BoujeeEnjinia1701/breathebox/cad/drawings/BBX-DWG-001.pdf

CONCEPT, NOT FOR FABRICATION | BreatheBox · github.com/BoujeeEnjinia1701/breathebox

FRONT VIEW
Scale 1:20; looking at the front (along +Y)

TOP VIEW
Scale 1:20; looking down (along -Z)

RIGHT VIEW
Scale 1:20; looking at the right side (along -X)

735

900 790

ISOMETRIC VIEW
Not to scale; adapter not shown; seen from the front right and above, about 30 deg elevation

KEY DIMENSIONS AND INTERFACES (MM)
Housing 510 x 560 x 250; 110 on sill, 400 into room Front view: outdoors at left; inner wall face at X = 0 Core 300 x 180 x 180, plate pitch 2.5
Insert panel 20 thick x 260 high, trims to 700 to 1000 Ports 150 x 170 at Y = +/-185
Hood mouths 130 wide, 420 clear; outer edge +/-340 Supply filter ePM1 50 % 150 x 170 x 25; exhaust G3 pad Fans 120 x 120 x 32 blowers, 24 V PWM with tach
Flow 30 to 70 m3/h per stream, 50 nominal, 32 night mode
Core frames, dividers and fan bulkhead seal the four air paths Tray drain at floor level, 12 x 8 tube through panel
Rails, struts and padded foot prop on the wall; foot 400 above floor Sash jammer (item 14) above the raised sash; not shown
Mass about 11.8 kg installed; build plan BBX-BLD-001 PRELIMINARY, NOT FOR FABRICATION
REV | DESCRIPTION | DATE | BY
P1 | Preliminary GA for TRL 3 (BBX-CAL-001) | 2026-09-25 | AC
P2 | Night mode note (BBX-DDR-002) | 2026-09-25 | AC
P3 | Constructable design (BBX-DDR-003) | 2026-09-30 | AC
P4 | Wall foot at 400; sash jammer (BBX-DEC-001) | 2026-10-02 | AC
BREATHEBOX | github.com/BoujeeEnjinia1701/breathebox

## General arrangement, window HRV

DRAWING NO.
BBX-DWG-001

REV
P4

SHEET
1 of 1

SIZE

## ANSI B

SCALE
1:20

UNITS
mm
PROJECTION | DATE
2026-10-02

DRAWN
Amish Chadha

MATERIAL / NOTES
Housing 6 mm PVC foam board, battens, foam lining; panel PVC/XPS; hoods PVC; bracket Al. See bom/bom.csv
Licensed CERN-OHL-S-2.0 · Design Molecule Lab · designmolecule.com | Generated from cad/src; do not edit by hand
