BoujeeEnjinia1701/breathebox/cad/drawings/BBX-DWG-111.pdf

BUILD PLAN SKETCH, PLAN NOT YET BUILT BreatheBox · github.com/BoujeeEnjinia1701/breathebox

FRONT VIEW
Scale 1:5; looking at the front (along +Y)

TOP VIEW
Scale 1:5; looking down (along -Z)

RIGHT VIEW
Scale 1:5; looking at the right side (along -X)

390

50 44

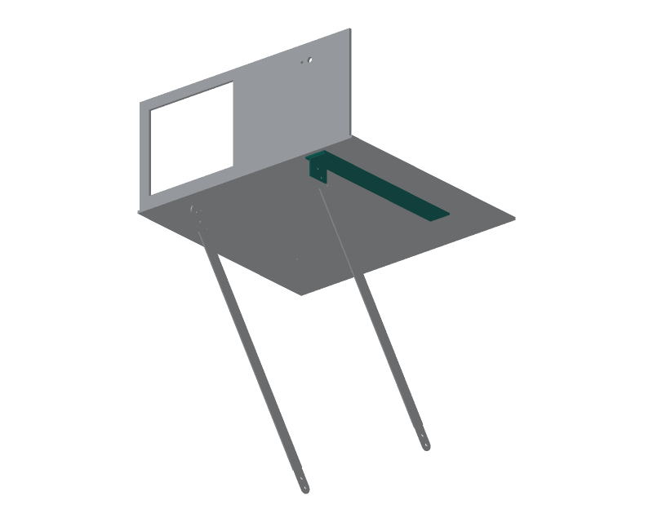
[picture p7: figure]

WHERE IT GOES
This part in colour, its neighbours in grey

HOW TO MAKE IT AND HOW IT FITS
Rail: 50 x 4 aluminium flat bar, 390 long. Round the corners.
Two 5.5 holes for the housing bolts, 30 and 330 from the wall end, 25 in from the rail's inner edge.
Two 5.5 holes countersunk from the top for the cleat, 348 and 378 from the wall end, 31 in from the inner edge.
Cleat: 40 x 40 x 3 angle, 50 long. Flat leg under the rail, 338 to 388 from the wall end, holes matching the rail. Upright leg on the rail's inner side: two 6.6 holes, 27 and 15.5 from the cleat's wall-side end, 16 and 32.4 down from the rail's underside. Drill the strut holes with the strut clamped in place (sketch 112). Fit: the rail bolts under the housing base with two M5 bolts, nuts inside under the floor lining; its wall end is flush with the housing's line on the wall face.
REV | DESCRIPTION | DATE | BY
P1 | Making sketch for the prototype build plan | 2026-09-30 | AC
P2 | Wall foot at 400 mm, longer struts (BBX-DEC-001) | 2026-10-02 | AC
BREATHEBOX | github.com/BoujeeEnjinia1701/breathebox

## BreatheBox bracket rail with its top cleat (make 2): making sketch

DRAWING NO.
BBX-DWG-111

REV
P2

SHEET
1 of 1

SIZE

## ANSI B

SCALE
1:5

UNITS
mm
PROJECTION | DATE
2026-10-02

DRAWN
Amish Chadha

MATERIAL / NOTES
Aluminium flat bar 50 x 4; equal angle 40 x 40 x 3
Licensed CERN-OHL-S-2.0 · Design Molecule Lab · designmolecule.com | Generated from cad/src; do not edit by hand
