BoujeeEnjinia1701/breathebox/cad/drawings/BBX-DWG-112.pdf

BUILD PLAN SKETCH, PLAN NOT YET BUILT BreatheBox · github.com/BoujeeEnjinia1701/breathebox

FRONT VIEW
Scale 1:5; looking at the front (along +Y)

TOP VIEW
Scale 1:5; looking down (along -Z)

RIGHT VIEW
Scale 1:5; looking at the right side (along -X)

621

26 20

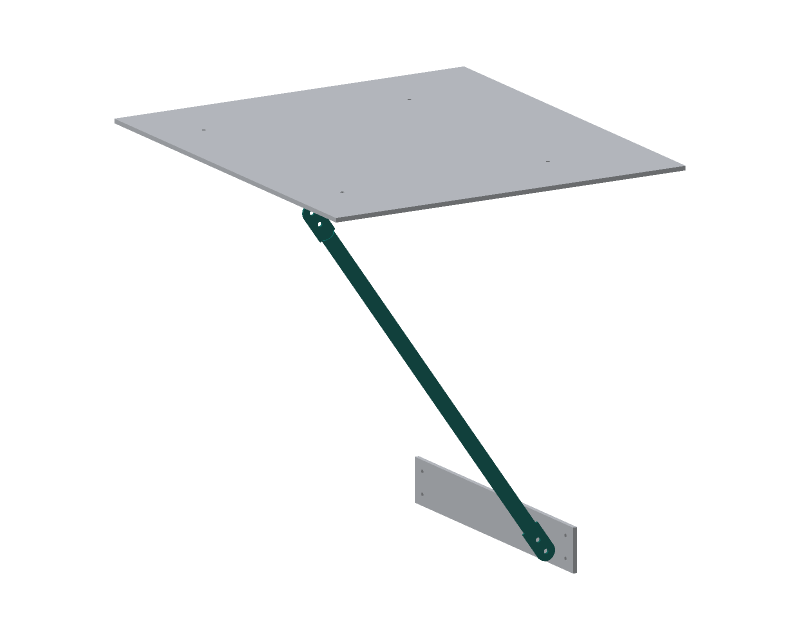
[picture p8: figure]

WHERE IT GOES
This part in colour, its neighbours in grey

HOW TO MAKE IT AND HOW IT FITS
Tube 20 x 1.5, cut 621 long.
Flatten 40 of each end in a vice between two flat bars, both flats in the same plane; anneal with a gas torch first if it cracks.
Trim each flat to 26 wide and round its end to a 13 radius about the end hole.
End holes 6.6, 595.3 apart; a second 6.6 hole 20 in
from each end hole, on the centre line. Two holes at each end make the joints rigid, so the bracket cannot fold.
The strut rises at 55 degrees from the wall foot to the rail. Drill the second pair with the strut clamped to both cleats, so all four holes line up.
Fit: M6 bolts, heads on the strut side, nyloc nuts on the cleats. Check: end holes within 0.5 of the length; flats not twisted.
REV | DESCRIPTION | DATE | BY
P1 | Making sketch for the prototype build plan | 2026-09-30 | AC
P2 | Wall foot at 400 mm, longer struts (BBX-DEC-001) | 2026-10-02 | AC
BREATHEBOX | github.com/BoujeeEnjinia1701/breathebox

## BreatheBox strut (make 2): making sketch

DRAWING NO.
BBX-DWG-112

REV
P2

SHEET
1 of 1

SIZE

## ANSI B

SCALE
1:5

UNITS
mm
PROJECTION | DATE
2026-10-02

DRAWN
Amish Chadha

MATERIAL / NOTES
Aluminium round tube 20 x 1.5 mm, 6063 class
Licensed CERN-OHL-S-2.0 · Design Molecule Lab · designmolecule.com | Generated from cad/src; do not edit by hand
