BoujeeEnjinia1701/breathebox/cad/drawings/BBX-DWG-113.pdf

BUILD PLAN SKETCH, PLAN NOT YET BUILT BreatheBox · github.com/BoujeeEnjinia1701/breathebox

FRONT VIEW
Scale 1:5; looking at the front (along +Y)

TOP VIEW
Scale 1:5; looking down (along -Z)

RIGHT VIEW
Scale 1:5; looking at the right side (along -X)

400

48 60

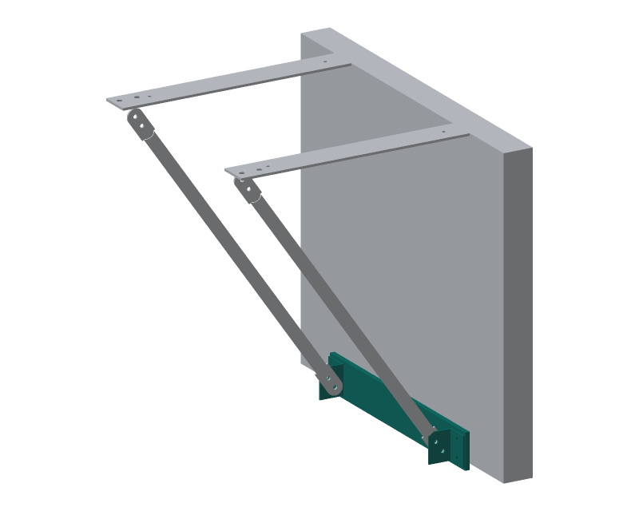
[picture p9: figure]

WHERE IT GOES
This part in colour, its neighbours in grey

HOW TO MAKE IT AND HOW IT FITS
Bar: 60 x 6 aluminium flat bar, 400 long. Four 5.5 holes, 181 each side of centre, 15 above and below its centre line, countersunk from the wall side so the screw heads sit flush.
Pad: 2 mm rubber sheet 400 x 60, glued to the wall side, with relief holes over the screw heads.
Cleats: 40 x 40 x 3 angle, 50 long. One leg on the bar's room face, holes matching the bar; the other leg points into the room, on the inner side, with two 6.6 holes 16 and 27.5 out from the bar face, 17 and 33.4 up from the cleat's lower end.
Fit: the foot's centre line is 400 above the floor; the pad presses on the wall; nothing is fixed to the wall.
Check: the pad lies flat on the wall over its whole length.
REV | DESCRIPTION | DATE | BY
P1 | Making sketch for the prototype build plan | 2026-09-30 | AC
P2 | Wall foot at 400 mm, longer struts (BBX-DEC-001) | 2026-10-02 | AC
BREATHEBOX | github.com/BoujeeEnjinia1701/breathebox

## BreatheBox wall foot with pad and foot cleats: making sketch

DRAWING NO.
BBX-DWG-113

REV
P2

SHEET
1 of 1

SIZE

## ANSI B

SCALE
1:5

UNITS
mm
PROJECTION | DATE
2026-10-02

DRAWN
Amish Chadha

MATERIAL / NOTES
Aluminium flat bar 60 x 6; angle 40 x 40 x 3; rubber 2 mm
Licensed CERN-OHL-S-2.0 · Design Molecule Lab · designmolecule.com | Generated from cad/src; do not edit by hand
