BoujeeEnjinia1701/breathebox/cad/drawings/BBX-DWG-101.pdf

BUILD PLAN SKETCH, PLAN NOT YET BUILT BreatheBox · github.com/BoujeeEnjinia1701/breathebox

FRONT VIEW
Scale 1:10; looking at the front (along +Y)

TOP VIEW
Scale 1:10; looking down (along -Z)

RIGHT VIEW
Scale 1:10; looking at the right side (along -X)

510

560 244

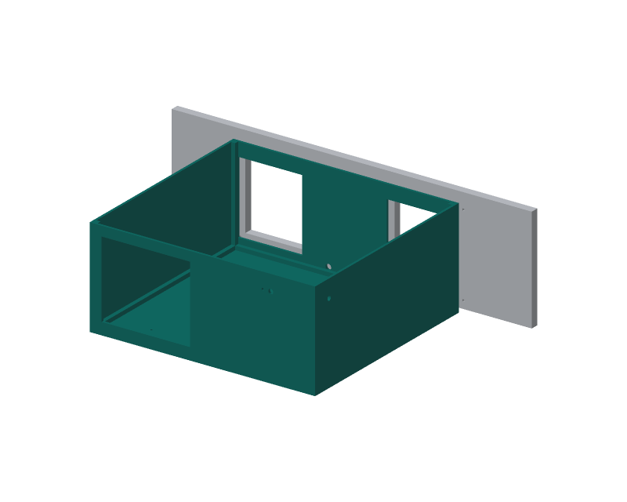
[picture p51: figure]

WHERE IT GOES
This part in colour, its neighbours in grey

HOW TO MAKE IT AND HOW IT FITS
Cut from 6 mm PVC foam board: base 510 x 560; two sides 510 x 238; two ends 548 x 238. Ends fit between the sides; all stand on the base. Outdoor end: two 160 x 180 openings centred 185 left and right, from 24 to 204 up from its bottom edge; a 14 hole 40 left, 16 up. Room end: a 220 x 190 opening from 30 to 250 left, 24 to 214 up; holes 6 and 12 at 150 and 170 right, 199 up (light and button).
Right side: a 12 hole 50 from the room end, 194 up (power gland). Base: four 5.5 holes, 140 and 440 from the outdoor edge, 175 each side. Battens 10 x 10: four uprights 238; two 478 under the sides; two 528 under the ends. Glue every joint with PVC cement and screw each board into the batten behind it, 3.5 x 16 screws at 80 centres.
Check: square within 1 mm on the diagonals; openings line up with the collar and grille positions on the other sketches.
REV | DESCRIPTION | DATE | BY
P1 | Making sketch for the prototype build plan | 2026-09-30 | AC
BREATHEBOX | github.com/BoujeeEnjinia1701/breathebox

## BreatheBox housing boards and battens: making sketch

DRAWING NO.
BBX-DWG-101

REV
P1

SHEET
1 of 1

SIZE

## ANSI B

SCALE
1:10

UNITS
mm
PROJECTION | DATE
2026-09-30

DRAWN
Amish Chadha

MATERIAL / NOTES
6 mm PVC foam board; 10 x 10 mm PVC or pine strip
Licensed CERN-OHL-S-2.0 · Design Molecule Lab · designmolecule.com | Generated from cad/src; do not edit by hand
