BoujeeEnjinia1701/breathebox/cad/drawings/BBX-DWG-102.pdf

BUILD PLAN SKETCH, PLAN NOT YET BUILT BreatheBox · github.com/BoujeeEnjinia1701/breathebox

FRONT VIEW
Scale 1:5; looking at the front (along +Y)

TOP VIEW
Scale 1:5; looking down (along -Z)

RIGHT VIEW
Scale 1:5; looking at the right side (along -X)

510

580 46

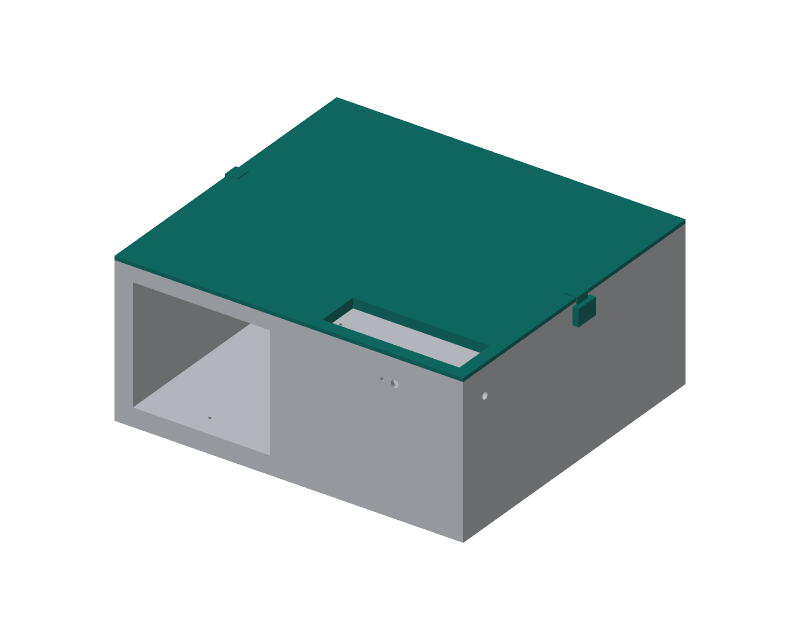
[picture p52: figure]

WHERE IT GOES
This part in colour, its neighbours in grey

HOW TO MAKE IT AND HOW IT FITS
Board 510 x 560 x 6 mm. Opening 70 x 220 for the supply grille,
420 to 490 from the outdoor edge, 40 to 260 right of centre.
Lining plug: 10 mm foam, 476 x 526, glued centred under the board so it drops inside the wall lining with 1 mm all round; cut the same
70 x 220 opening through it.
Foam blocks glued under the plug (they hold the core and filters): core hold-down 306 long x 168 wide x 24 deep, over the core; supply filter block 34 x 138 x 28 at the outdoor end, right; exhaust filter block 21 x 200 x 18 at the room end, left.
Latch keepers: one each side, 118 to 142 from the outdoor edge. Check: the lid drops on with the plug inside the walls and the latches pull it down evenly onto the gasket tape.
REV | DESCRIPTION | DATE | BY
P1 | Making sketch for the prototype build plan | 2026-09-30 | AC
BREATHEBOX | github.com/BoujeeEnjinia1701/breathebox

## BreatheBox lid: making sketch

DRAWING NO.
BBX-DWG-102

REV
P1

SHEET
1 of 1

SIZE

## ANSI B

SCALE
1:5

UNITS
mm
PROJECTION | DATE
2026-09-30

DRAWN
Amish Chadha

MATERIAL / NOTES
6 mm PVC foam board; 10 mm closed-cell foam
Licensed CERN-OHL-S-2.0 · Design Molecule Lab · designmolecule.com | Generated from cad/src; do not edit by hand
