BoujeeEnjinia1701/breathebox/cad/drawings/BBX-DWG-103.pdf

BUILD PLAN SKETCH, PLAN NOT YET BUILT BreatheBox · github.com/BoujeeEnjinia1701/breathebox

FRONT VIEW
Scale 1:5; looking at the front (along +Y)

TOP VIEW
Scale 1:5; looking down (along -Z)

RIGHT VIEW
Scale 1:5; looking at the right side (along -X)

528

3 218

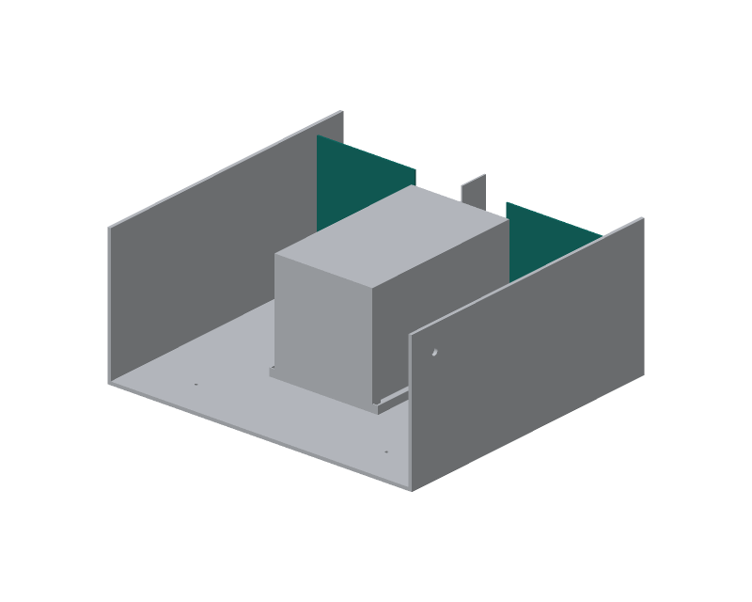
[picture p53: figure]

WHERE IT GOES
This part in colour, its neighbours in grey

HOW TO MAKE IT AND HOW IT FITS
Make two from 3 mm PVC foam board, each 528 wide x 218 tall. Cut a U 168 wide, centred, from 20 up off the bottom edge to the top. The core's 180 wide end then overlaps the U by 6 each side and 6
at the bottom; stick 3 mm foam gasket tape round the U on the
core side.
Outdoor frame only: a 13 hole 40 left of centre (as seen from the room; drawn here as seen from outdoors), 6 up, for the drain tube.
Fit: stands on the floor lining, glued to the side lining with
contact adhesive, 300 apart (inside faces) so the core fits
between them; the lid's foam block closes the U above the core. Check: the core drops between the frames without force and both ends bear on the gasket all round the U.
REV | DESCRIPTION | DATE | BY
P1 | Making sketch for the prototype build plan | 2026-09-30 | AC
BREATHEBOX | github.com/BoujeeEnjinia1701/breathebox

## BreatheBox core frame (make 2): making sketch

DRAWING NO.
BBX-DWG-103

REV
P1

SHEET
1 of 1

SIZE

## ANSI B

SCALE
1:5

UNITS
mm
PROJECTION | DATE
2026-09-30

DRAWN
Amish Chadha

MATERIAL / NOTES
3 mm PVC foam board
Licensed CERN-OHL-S-2.0 · Design Molecule Lab · designmolecule.com | Generated from cad/src; do not edit by hand
