BoujeeEnjinia1701/breathebox/cad/drawings/BBX-DWG-104.pdf

BUILD PLAN SKETCH, PLAN NOT YET BUILT BreatheBox · github.com/BoujeeEnjinia1701/breathebox

FRONT VIEW
Scale 1:2; looking at the front (along +Y)

TOP VIEW
Scale 1:2; looking down (along -Z)

RIGHT VIEW
Scale 1:2; looking at the right side (along -X)

236

3 218

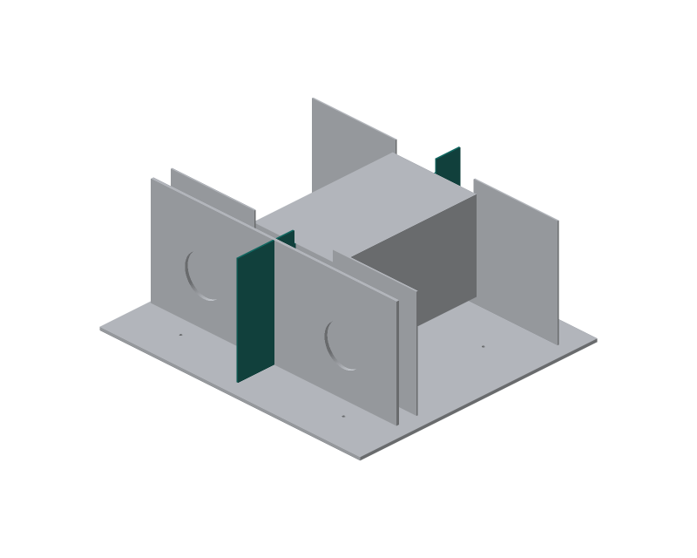
[picture p54: figure]

WHERE IT GOES
This part in colour, its neighbours in grey

HOW TO MAKE IT AND HOW IT FITS
Three pieces of 3 mm PVC foam board, all 218 tall, on the centre line. Outdoor-end divider: 51 long, plus a tongue 3 long x 174 tall,
20 up from the bottom, that reaches through the frame's U to the core face (drawn left).
Core-side divider: 37 long plus the same tongue (drawn middle). Room-side divider: 78 long, plain (drawn right).
Fit: each stands on the floor lining, glued to the frame, bulkhead or end lining it meets; the tongue's end just touches the core. The dividers split each end of the box into supply (right) and exhaust (left), so the two air streams never meet.
Check: no daylight past any divider edge with the core in.
REV | DESCRIPTION | DATE | BY
P1 | Making sketch for the prototype build plan | 2026-09-30 | AC
BREATHEBOX | github.com/BoujeeEnjinia1701/breathebox

## BreatheBox dividers (3): making sketch

DRAWING NO.
BBX-DWG-104

REV
P1

SHEET
1 of 1

SIZE

## ANSI B

SCALE
1:2

UNITS
mm
PROJECTION | DATE
2026-09-30

DRAWN
Amish Chadha

MATERIAL / NOTES
3 mm PVC foam board
Licensed CERN-OHL-S-2.0 · Design Molecule Lab · designmolecule.com | Generated from cad/src; do not edit by hand
