BoujeeEnjinia1701/breathebox/cad/drawings/BBX-DWG-105.pdf

BUILD PLAN SKETCH, PLAN NOT YET BUILT BreatheBox · github.com/BoujeeEnjinia1701/breathebox

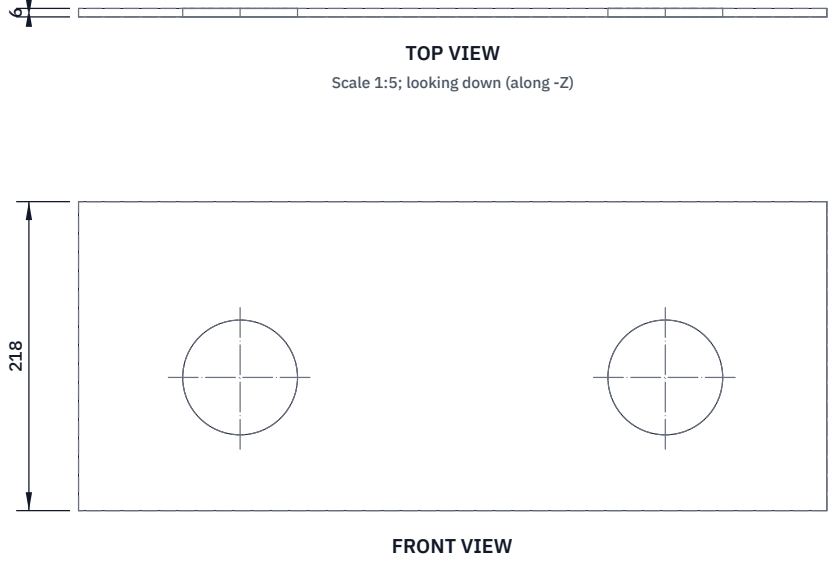
[picture p55: figure]
FRONT VIEW; TOP VIEW; Scale 1:5; looking down (along -Z)

Scale 1:5; looking at the front (along +Y)

RIGHT VIEW
Scale 1:5; looking at the right side (along -X)

528

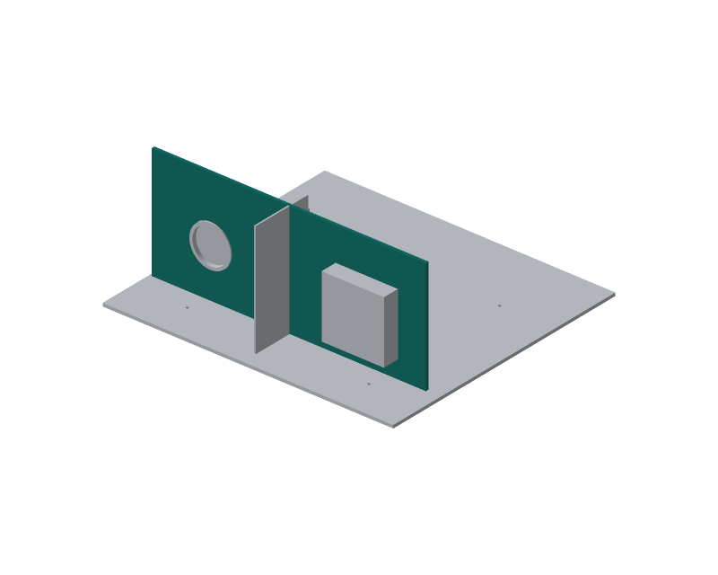
[picture p56: figure]

WHERE IT GOES
This part in colour, its neighbours in grey

HOW TO MAKE IT AND HOW IT FITS
6 mm PVC foam board, 528 wide x 218 tall.
Two 81 holes for the fan inlets, centred 150 left and 150 right of centre, 94 up from the bottom edge.
Mark each fan's four mounting holes through the fan itself; drill 5 and fit rubber grommets so the fans do not drum on the board. Fit: stands on the floor lining, its room-side face 94 from the outside of the room end (78 from the end lining), glued to the side linings. Drawn as seen from outdoors.
The supply fan (right) goes on the room side, its inlet through the hole; the exhaust fan (left) goes on the core side, its inlet through the hole facing the room. M4 nylon screws.
Check: each fan ring sits in its hole with about 0.5 mm all round.
REV | DESCRIPTION | DATE | BY
P1 | Making sketch for the prototype build plan | 2026-09-30 | AC
BREATHEBOX | github.com/BoujeeEnjinia1701/breathebox

## BreatheBox fan bulkhead: making sketch

DRAWING NO.
BBX-DWG-105

REV
P1

SHEET
1 of 1

SIZE

## ANSI B

SCALE
1:5

UNITS
mm
PROJECTION | DATE
2026-09-30

DRAWN
Amish Chadha

MATERIAL / NOTES
6 mm PVC foam board
Licensed CERN-OHL-S-2.0 · Design Molecule Lab · designmolecule.com | Generated from cad/src; do not edit by hand
