BoujeeEnjinia1701/breathebox/cad/drawings/BBX-DWG-106.pdf

BUILD PLAN SKETCH, PLAN NOT YET BUILT BreatheBox · github.com/BoujeeEnjinia1701/breathebox

FRONT VIEW
Scale 1:2; looking at the front (along +Y)

TOP VIEW
Scale 1:2; looking down (along -Z)

RIGHT VIEW
Scale 1:2; looking at the right side (along -X)

164

35 218

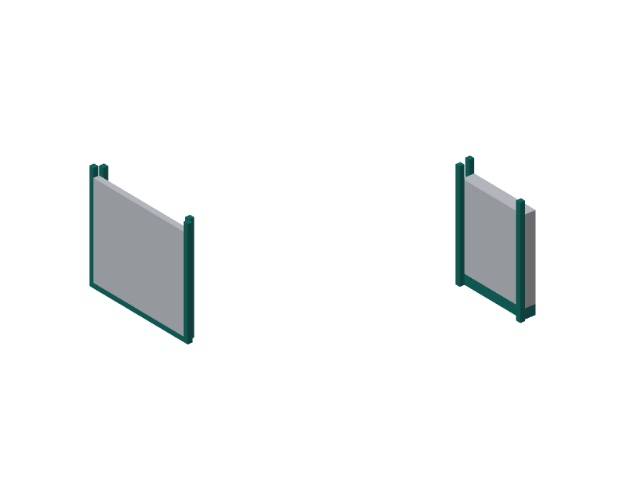
[picture p57: figure]

WHERE IT GOES
This part in colour, its neighbours in grey

HOW TO MAKE IT AND HOW IT FITS
All 10 x 10 strip, glued to the lining with contact adhesive.
Supply seat (outdoor end, right; drawn here): a side strip 218 long against the end lining beside the filter's left edge; two lip
strips 218 long 25 out from the end lining, lapping 6 over each filter edge; a bottom stop 150 x 25 x 20 under the filter.
Exhaust seat (room end, left): side strips 218 long each side of the pad against the room end lining; lip strips 12 out from it, lapping 10 over each pad edge; a bottom stop 220 x 12 x 10. The air pushes each filter onto its lips; the lid's foam blocks press on the top edges, so no air goes round a filter.
Check: each filter slides down into its seat by hand and sits square on its lips and stop.
REV | DESCRIPTION | DATE | BY
P1 | Making sketch for the prototype build plan | 2026-09-30 | AC
BREATHEBOX | github.com/BoujeeEnjinia1701/breathebox

## BreatheBox filter seat strips and stops: making sketch

DRAWING NO.
BBX-DWG-106

REV
P1

SHEET
1 of 1

SIZE

## ANSI B

SCALE
1:2

UNITS
mm
PROJECTION | DATE
2026-09-30

DRAWN
Amish Chadha

MATERIAL / NOTES
10 x 10 mm PVC or pine strip
Licensed CERN-OHL-S-2.0 · Design Molecule Lab · designmolecule.com | Generated from cad/src; do not edit by hand
