BoujeeEnjinia1701/breathebox/cad/drawings/BBX-DWG-107.pdf

BUILD PLAN SKETCH, PLAN NOT YET BUILT BreatheBox · github.com/BoujeeEnjinia1701/breathebox

FRONT VIEW
Scale 1:5; looking at the front (along +Y)

TOP VIEW
Scale 1:5; looking down (along -Z)

RIGHT VIEW
Scale 1:5; looking at the right side (along -X)

300

200 14

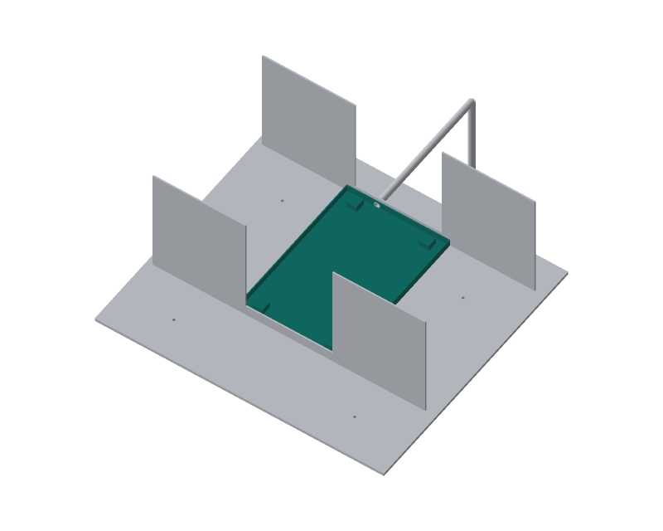
[picture p58: figure]

WHERE IT GOES
This part in colour, its neighbours in grey

HOW TO MAKE IT AND HOW IT FITS
2 mm PETG sheet. Blank 328 x 228; fold up 14 mm on all four sides (heat gun and a wooden former), so the tray is 300 x 200 x 14. Seal each corner inside with a fillet of clear silicone.
Drain hole 12 in the outdoor end wall, 40 left of centre, its
centre 6 up from the underside so the bore is flush with the floor. Four pads 20 x 20 x 12 cut from PETG offcuts stacked and glued, at the four corners, 10 in from each end and 60 out from the centre line; the core sits on them, so water runs freely underneath.
Fit: sits on the floor lining between the core frames.
Check: fill with 100 ml of water with the drain tube fitted; it all runs out with the box level, and no corner weeps.
REV | DESCRIPTION | DATE | BY
P1 | Making sketch for the prototype build plan | 2026-09-30 | AC
BREATHEBOX | github.com/BoujeeEnjinia1701/breathebox

## BreatheBox condensate tray: making sketch

DRAWING NO.
BBX-DWG-107

REV
P1

SHEET
1 of 1

SIZE

## ANSI B

SCALE
1:5

UNITS
mm
PROJECTION | DATE
2026-09-30

DRAWN
Amish Chadha

MATERIAL / NOTES
PETG sheet 2 mm
Licensed CERN-OHL-S-2.0 · Design Molecule Lab · designmolecule.com | Generated from cad/src; do not edit by hand
