BoujeeEnjinia1701/breathebox/cad/drawings/BBX-DWG-108.pdf

BUILD PLAN SKETCH, PLAN NOT YET BUILT BreatheBox · github.com/BoujeeEnjinia1701/breathebox

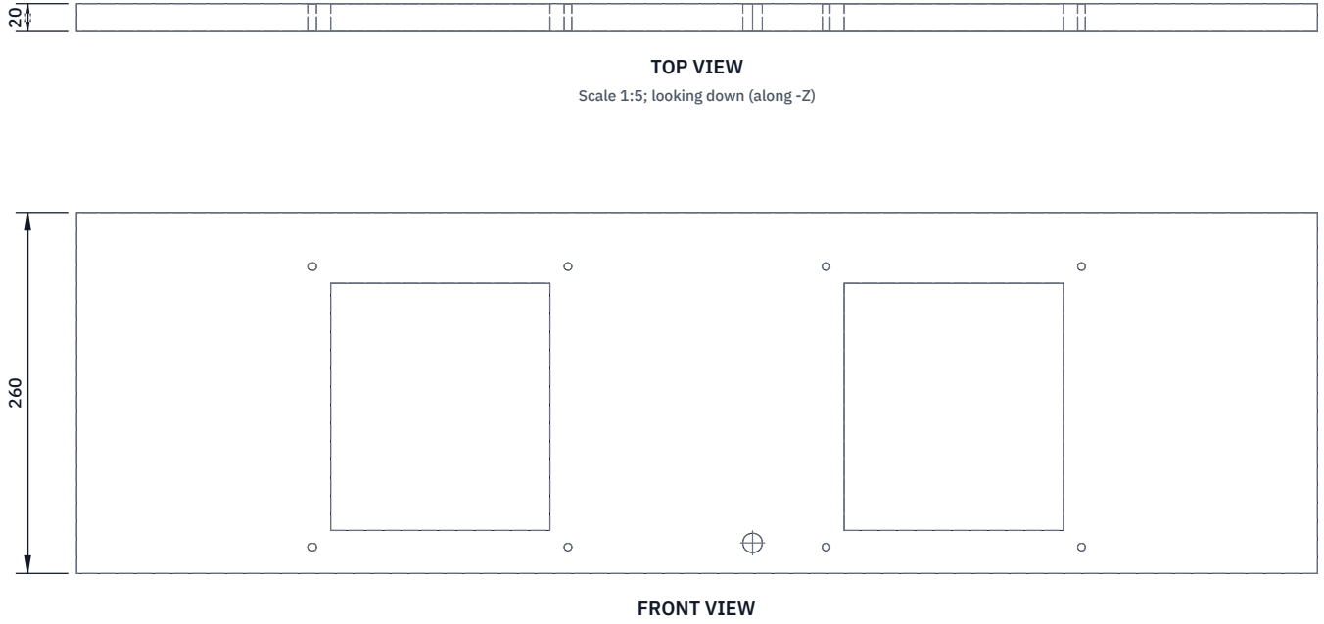
[picture p59: figure]
FRONT VIEW; TOP VIEW; Scale 1:5; looking down (along -Z)

Scale 1:5; looking at the front (along +Y)

RIGHT VIEW
Scale 1:5; looking at the right side (along -X)

894

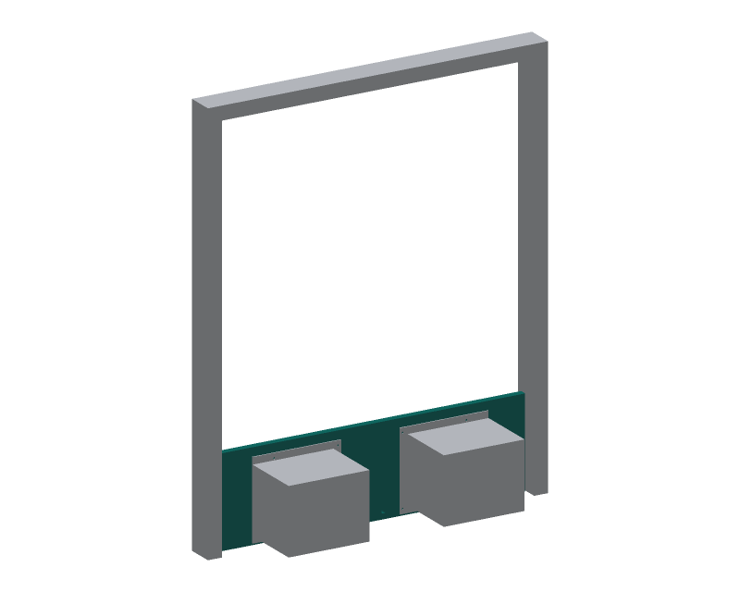
[picture p60: figure]

WHERE IT GOES
This part in colour, its neighbours in grey

HOW TO MAKE IT AND HOW IT FITS
20 mm panel, 260 tall, cut to the window's clear width less 6 (894 for a 900 window), so the EPDM seals take up 3 each end. Two 158 x 178 cut-outs centred 185 left and right of centre, from 31 to 209 up from the bottom edge.
Drain hole 14, 40 left of centre as seen from the room, 22 up (drawn as seen from outdoors, so it appears right of centre).
Bolt holes 5.5: at 93 and 277 out from centre on each side, 19 and 221 up (eight in all). Drill them through the collar flange
clamped in place, so they match.
Seal the cut edges of the XPS core with aluminium tape.
Fit: stands on the sill in the lower sash's track; the raised sash closes down on its top edge.
Check: slides into the track with the seals just touching the jambs.
REV | DESCRIPTION | DATE | BY
P1 | Making sketch for the prototype build plan | 2026-09-30 | AC
BREATHEBOX | github.com/BoujeeEnjinia1701/breathebox

## BreatheBox window insert panel: making sketch

DRAWING NO.
BBX-DWG-108

REV
P1

SHEET
1 of 1

SIZE

## ANSI B

SCALE
1:5

UNITS
mm
PROJECTION | DATE
2026-09-30

DRAWN
Amish Chadha

MATERIAL / NOTES
20 mm panel, PVC foam skins over XPS
Licensed CERN-OHL-S-2.0 · Design Molecule Lab · designmolecule.com | Generated from cad/src; do not edit by hand
