BoujeeEnjinia1701/breathebox/cad/drawings/BBX-DWG-109.pdf

BUILD PLAN SKETCH, PLAN NOT YET BUILT BreatheBox · github.com/BoujeeEnjinia1701/breathebox

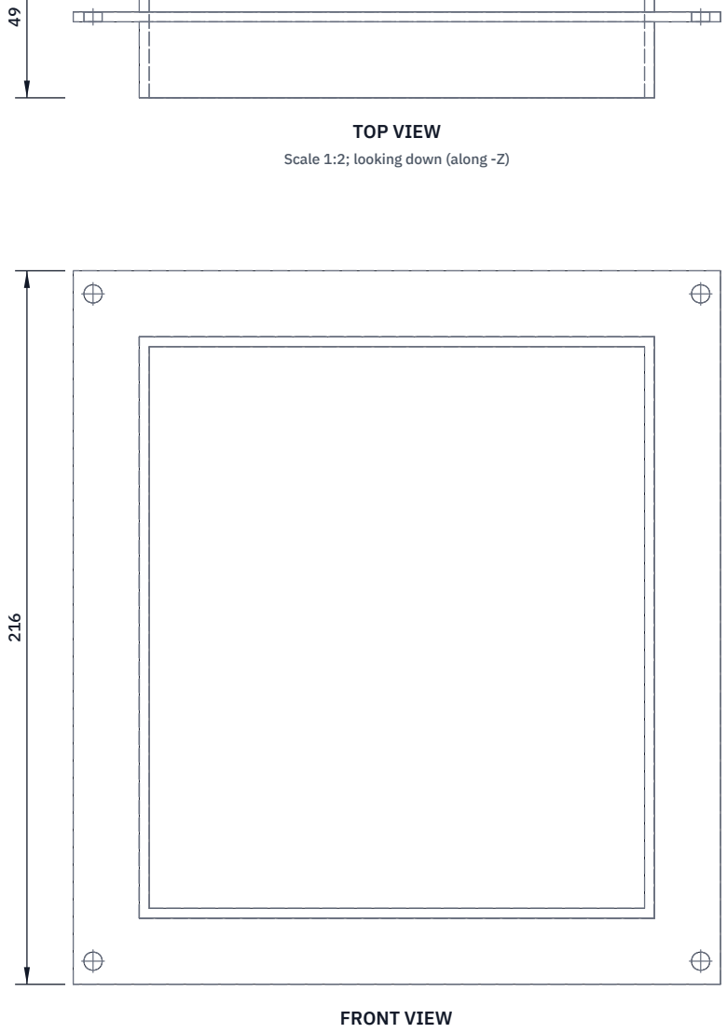
[picture p61: figure]
FRONT VIEW; TOP VIEW; Scale 1:2; looking down (along -Z)

Scale 1:2; looking at the front (along +Y)

RIGHT VIEW
Scale 1:2; looking at the right side (along -X)

196

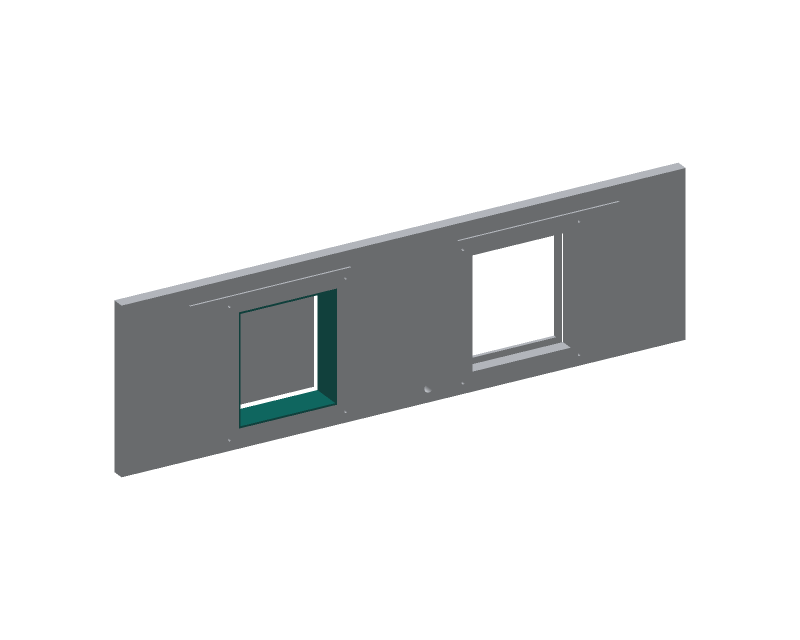
[picture p62: figure]

WHERE IT GOES
This part in colour, its neighbours in grey

HOW TO MAKE IT AND HOW IT FITS
A rectangular tube, bore 150 x 170, from four strips of 3 mm PVC glued with PVC cement: two 49 x 156 and two 49 x 170.
49 is the design-case length: cut it so the collar reaches from
the hood plate's outside face to the housing's end lining.
Flange: a 3 mm PVC frame 196 x 216 with a 156 x 176 hole, glued round the tube 23 from its outdoor end.
Four 5.5 holes in the flange, 6 in from the long edges and 7 in from the short edges (at its corners).
Fit: the outdoor end goes through the panel cut-out into the hood back plate; the flange lies on the panel's room face; four M5 bolts clamp flange, panel and hood plate. The room end slides 6 into the housing opening on 2 mm foam gasket.
Check: bore square; flange flat on the panel.
REV | DESCRIPTION | DATE | BY
P1 | Making sketch for the prototype build plan | 2026-09-30 | AC
BREATHEBOX | github.com/BoujeeEnjinia1701/breathebox

## BreatheBox collar (make 2): making sketch

DRAWING NO.
BBX-DWG-109

REV
P1

SHEET
1 of 1

SIZE

## ANSI B

SCALE
1:2

UNITS
mm
PROJECTION | DATE
2026-09-30

DRAWN
Amish Chadha

MATERIAL / NOTES
3 mm rigid PVC sheet
Licensed CERN-OHL-S-2.0 · Design Molecule Lab · designmolecule.com | Generated from cad/src; do not edit by hand
