BoujeeEnjinia1701/breathebox/cad/drawings/BBX-DWG-110.pdf

BUILD PLAN SKETCH, PLAN NOT YET BUILT BreatheBox · github.com/BoujeeEnjinia1701/breathebox

FRONT VIEW
Scale 1:5; looking at the front (along +Y)

TOP VIEW
Scale 1:5; looking down (along -Z)

RIGHT VIEW
Scale 1:5; looking at the right side (along -X)

255

183 230

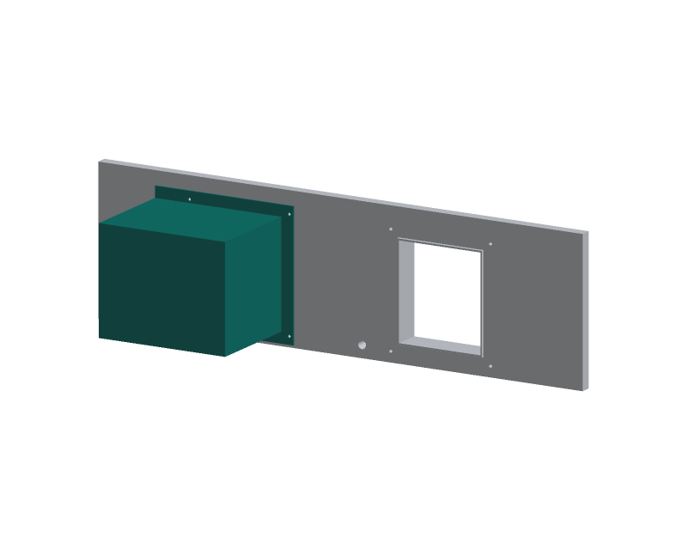
[picture p63: figure]

WHERE IT GOES
This part in colour, its neighbours in grey

HOW TO MAKE IT AND HOW IT FITS
Back plate: 3 mm PVC, 255 wide x 230 tall, with a 156 x 176 hole for the collar and four 5.5 holes matching the collar flange.
Hood box from 3 mm PVC, glued to the plate's outer face: top 180 x 233, two sides 180 x 187, outer end 233 x 187; open at the back (onto the plate) and at the bottom over the outer 124 mm of
its width (the mouth); the inner 106 mm of the bottom is closed. Mesh: 1 mm stainless mesh over the mouth, held by 10 mm PVC strips glued inside the mouth edges.
The two hoods are mirror images; mouths face down and point outward, 420 apart.
Fit: the collar glues into the plate's hole; the plate is bolted through the panel with the collar flange behind it.
Check: water poured on the top runs off, none enters the mouth.
REV | DESCRIPTION | DATE | BY
P1 | Making sketch for the prototype build plan | 2026-09-30 | AC
BREATHEBOX | github.com/BoujeeEnjinia1701/breathebox

## BreatheBox hood with back plate (make 2): making sketch

DRAWING NO.
BBX-DWG-110

REV
P1

SHEET
1 of 1

SIZE

## ANSI B

SCALE
1:5

UNITS
mm
PROJECTION | DATE
2026-09-30

DRAWN
Amish Chadha

MATERIAL / NOTES
3 mm rigid PVC sheet; 1 mm stainless mesh
Licensed CERN-OHL-S-2.0 · Design Molecule Lab · designmolecule.com | Generated from cad/src; do not edit by hand
