BoujeeEnjinia1701/breathebox/cad/drawings/BBX-DWG-114.pdf

BUILD PLAN SKETCH, PLAN NOT YET BUILT BreatheBox · github.com/BoujeeEnjinia1701/breathebox

FRONT VIEW
Scale 1:2; looking at the front (along +Y)

TOP VIEW
Scale 1:2; looking down (along -Z)

RIGHT VIEW
Scale 1:2; looking at the right side (along -X)

240

2 210

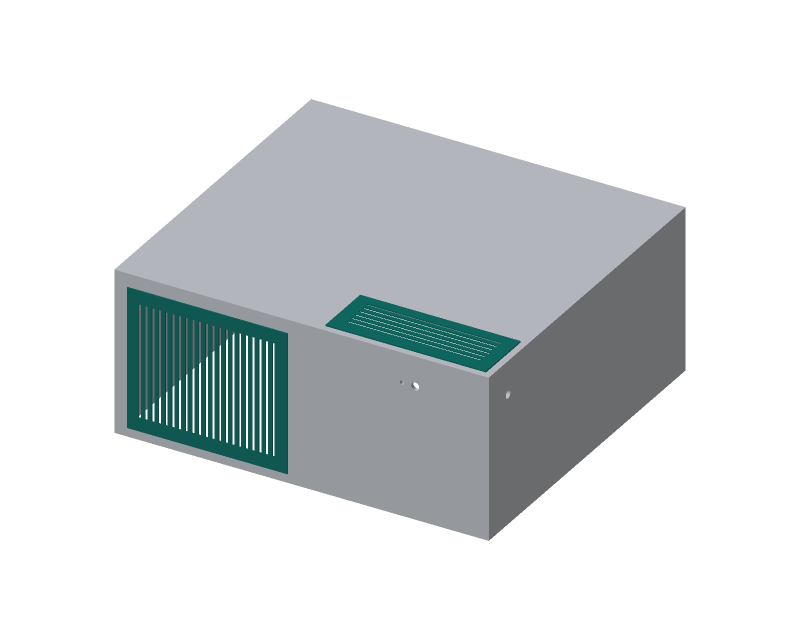
[picture p64: figure]

WHERE IT GOES
This part in colour, its neighbours in grey

HOW TO MAKE IT AND HOW IT FITS
Exhaust grille (room face, drawn): 240 wide x 210 tall, 21 slots
4 wide x 170 long at 10 centres. Supply grille (lid): 90 x 240,
6 slots 4 wide x 200 long at 10 centres.
Or buy perforated aluminium sheet with holes no larger than 5 mm and cut it to the same sizes.
Drill a 4.5 hole 6 in from each corner; deburr every edge.
Fit: each grille covers its opening with 10 to spare all round,
held by four M4 bolts with nuts inside the box.
The grilles keep fingers off the fans: no opening wider than 5. Check: a pencil cannot pass through any slot.
REV | DESCRIPTION | DATE | BY
P1 | Making sketch for the prototype build plan | 2026-09-30 | AC
BREATHEBOX | github.com/BoujeeEnjinia1701/breathebox

## BreatheBox grilles (2): making sketch

DRAWING NO.
BBX-DWG-114

REV
P1

SHEET
1 of 1

SIZE

## ANSI B

SCALE
1:2

UNITS
mm
PROJECTION | DATE
2026-09-30

DRAWN
Amish Chadha

MATERIAL / NOTES
Aluminium sheet 1.5 to 2 mm
Licensed CERN-OHL-S-2.0 · Design Molecule Lab · designmolecule.com | Generated from cad/src; do not edit by hand
