BoujeeEnjinia1701/breathebox/docs/pdf/BBX-PRC-001_v0.9.pdf

B R E AT H E B OX · D E S I G N P R E C I S

# BreatheBox design precis

Design Molecule Lab · designmolecule.com

D O C U M E N T CO N T RO L

Document ID | BBX-PRC-001 | Version | 0.9
Status | Draft | Date | 2026-10-02
Author | Amish Chadha | License | CERN-OHL-S-2.0
Project TRL | TRL 3 | Proof of concept
Repository | github.com/BoujeeEnjinia1701/breathebox
Source | docs/02-concept.md @ uncommitted

R EV I S I O N H I STO RY

Version | Date | Author | Change
0.9 | 2026-10-02 | Amish Chadha | Fan position and sash jammer decided by Amish on 2026-10-02 (BBX- DEC-001)
0.8 | 2026-10-01 | Amish Chadha | BioMedical area (BBX-DEC-001 v0.3); safety states a research and educational prototype, not a medical device
0.7 | 2026-10-01 | Amish Chadha | Budget treated as a value-engineering target
0.6 | 2026-09-30 | Amish Chadha | Design made constructable (BBX- DDR-003, open for Amish's review); components, mass, power and cost updated; build plan BBX-BLD-001 and register BBX-DEC-001 added
0.5 | 2026-09-26 | Amish Chadha | Budget approved by Amish; parts cost now within the $255 budget
0.4 | 2026-09-25 | Amish Chadha | Recommendations accepted by Amish (DDR-002)
0.3 | 2026-09-25 | Amish Chadha

TRL 3 update; numbers from BBX-CAL-001, layout from the parametric model and BBX-DWG-001, larger fans, design choices adopted for TRL 3 per

D R A F T · N O T F O R F A B R I C A T I O N

BBX-DDR-001 (open for Amish's review)

0.2 | 2026-09-25 | Amish Chadha | Populate to TRL 2 (architecture, first- order numbers, safety, media)
0.1 | 2026-09-25 | Amish Chadha | Initial scaffold

## BreatheBox design precis

### Summary

BreatheBox is a single-room heat recovery ventilator that sits on the sill of a sash window. Two small 24 V blowers push stale room air out and draw fresh air in through a counterflow plate core, so the incoming air picks up about 80 % of the heat (or, in summer, the cool) of the outgoing air. The TRL 3 calculations (BBX-CAL-001) give, for a bedroom at 50 m³/h and 0 °C outdoors: about 267 W of heat kept in the room for about 5.7 W of fan and control power, supply air at about 16 °C, and CO2 near 980 ppm overnight with two sleepers. One requirement is not met, noise (about 39 dB(A) at 1 m at 50 m³/h against 30 dB(A)), and cost is $28 over the value-engineering target (parts $283 against the $255 target, after the design was made constructable). A quiet night mode at 32 m³/h brings the noise estimate to about 30 dB(A) with clean filters. All figures are paper estimates; nothing has been built.

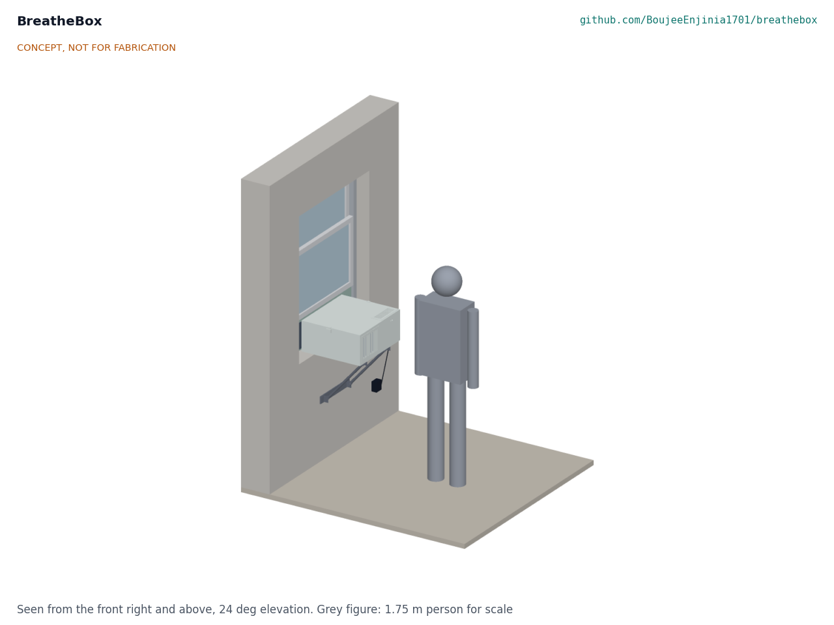
[picture p75: figure]

Figure 1. Parametric model on a sash window, with a 1.75 m person for scale.

### How it works

Mount. A 20 mm insulated panel fills the gap under the raised lower sash, which closes down onto it and is locked. The housing (510 x 560 x 250 mm) rests 110 mm on the sill and projects 400 mm into the room, where a bracket of two rails and two struts, propped on the wall by a padded foot, carries it; nothing is drilled.
Exhaust path. Room air enters a front grille, passes a coarse filter, and the exhaust fan blows it through one set of core channels, across the outdoor plenum and out of a downward-facing hood.
Supply path. Outdoor air enters the second hood, 420 mm from the exhaust mouth, passes through a collar in the panel and an ePM1 filter, and flows through the other set of core channels. The supply fan draws it through the core and blows it into the room through a top grille that throws air up and away from the occupant. Recover. The two streams flow in opposite directions on each side of thin polymer plates, so heat passes across without the air mixing.
Drain. In winter, moisture from the room air condenses in the core. A tray under the core falls to the outdoor side, and a tube carries the water through the panel and down the outside wall.
Control. A small controller reads CO2, humidity and temperature at the room intake and runs the fans between 30 and 70 m³/h, using the fan tach signals to keep the two streams within 10 %. A temperature probe at the core's exhaust outlet triggers a frost mode that slows the supply fan when the cold corner of the core nears 0 °C. Readings show on a status LED and, optionally, on a local web page; nothing needs the cloud. The firmware rules accepted in BBX-DDR-002 are: a quiet night mode that holds both streams at 32 m³/h and suppresses the CO2 boost; a speed cap at what 80 m³/h needs, so the worst-case draw stays under the 36 W adapter; and frost mode taking priority over both.

1.

2.

3.

4.

5.

6.


Figure 2. Cutaway through the supply side: hood and collar (outdoors, left), insert panel, supply filter, core over the condensate tray, supply fan and controller.
The general arrangement is drawing BBX-DWG-001 (Rev P3) in | cad/drawings/ , generated from | cad/src/
model.py . How to build the prototype, component by component, is in the build plan BBX-BLD-001 ( docs/05-build-plan.md ); BBX-DDR-003 records the changes that made the concept buildable, and the design decisions register BBX-DEC-001 ( docs/06-design-decisions.md ) lists what is still open.

### Main components

Table 1. Main components. Numbers match | bom/bom.csv | and Figure 4.

# | Component | Choice for TRL 3 | Notes

1 | Insulated housing | 6 mm PVC foam board on corner battens with 10 mm foam lining, 510 x 560 x 250 mm; core frames, dividers and a fan bulkhead for the four air paths; filter seats; two slotted grilles | Lift-off lid with two latches
2 | Counterflow core | Polymer plate core 180 x 180 x 300 mm, about 2.5 mm plate pitch | Bought spare-part HRV core; washable

3,

4 | Supply and exhaust fans | 24 V brushless centrifugal blowers, 120 x 120 x 32 mm class, about 100 m³/h free air and 400 Pa shut-off, PWM with tach | Larger than at TRL 2 (see BBX-CAL-001 section 4)
5 | Supply filter | ISO 16890 ePM1 50 % pleated panel, 150 x 170 x 25 mm, at the supply port | Replace about every 6 months or at twice the clean pressure drop
6 | Exhaust filter | Coarse washable pad, 220 x 190 mm | Keeps lint off the core
7 | Controller | ESP32-C3 class module with a Sensirion SCD41 class CO2, humidity and temperature sensor and two NTC probes | Check the sensor on the lab's CalRig before use
8 | Condensate tray and drain | PETG tray under the core, 12 x 8 mm tube to outdoors from the tray floor | Tube falls outdoors
9 | Window insert panel | 20 mm insulated panel with EPDM edge seals, trimmed to 700 to 1,000 mm | Raised sash held down on it by a bought no-drill sash jammer in the inner track (decided 2026-10-02)

10 Outdoor hoods

| and collars | Two PVC hoods on back plates with 1 mm stainless mesh on 130 mm wide mouths, 420 mm apart; flanged collars bolted through the panel | Mouths face down
11 Sill bracket | Two aluminium rails under the housing and two tube struts,
bolted rigid, to a padded wall foot

Props on the wall; no drilling

12 Power supply Certified 24 V, 1.5 A plug-in adapter; 2 A fuse on the 24 V input

No mains wiring in the unit

### Key numbers

All values come from BBX-CAL-001 and docs/04-calcs/sizing.py , with the assumptions stated there. They are estimates for a paper design.
Table 2. Key numbers at TRL 3.

Quantity | Estimate | Requirement
Core effectiveness | 79.8 % at 50 m³/h; 73.8 % at 70 m³/h | R2 met on paper
Heat recovered at 0 °C outdoors, 50 m³/h | 267 W of 335 W; 68 W lost; supply air 16.0 °C
Supply pressure drop at 50 m³/h | 52.3 Pa clean, 79.6 Pa with loaded filter
Flow limit at full fan speed | 80 m³/h per stream with loaded filters | R1 met on paper
Fan and control power | 5.7 W at 50 m³/h (7.5 W loaded); 14.8 W at 70 m³/h loaded | R3 met on paper
Noise at 1 m | About 39 dB(A) at 50 m³/h; night mode at 32 m³/h about 30 dB(A) clean, 32 dB(A) with loaded filters | R6 not met (written for 50 m³/h)
Heating-season energy kept | About 1,123 kWh for 29 kWh of fan energy (3,500 K·d)
CO2, two sleepers, 30 m³ room | 980 ppm overnight and 607 ppm 24 h mean at 50 m³/h; about 1,300 ppm overnight and 712 ppm 24 h mean in night mode | R4 met on paper
Condensate, upper bound | 0.21 L/h (70 m³/h, -3 °C) | R7 drain sized
Frost onset | About -2.2 °C outdoors at 50 m³/h
Frost mode at -10 °C | Supply slowed to 33 % of exhaust; about 2.2 Pa room depressurization through a door undercut | R7 met on paper
Clear distance between hood mouths | 420 mm; hoods fit windows from 686 mm clear width | R11, R8 met on paper
Unit mass | About 11.4 kg installed (11.7 kg with adapter) | R9 mass met on paper
Parts cost | $283 | R15 over the value-engineering target by $28 ($255 target)

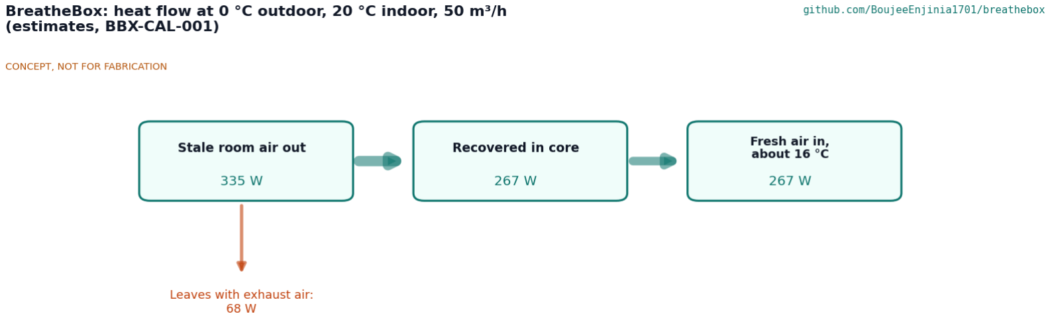
[picture p76: figure]

Figure 3. Heat flow in the design case (estimates from BBX-CAL-001).

### Key design choices

Each choice below was recommended at TRL 2 (BBX-DDR-001) and decided by Amish on 2026-09-25: go with recommendation (BBX-DDR-002).
Window insert rather than wall core; sash windows first (item A2). Renters can install it, and it comes out without a trace. The first version fits vertical sliding sash windows from 700 to 1,000 mm clear width, with an adapter for horizontal sliders. Casement and tilt-and-turn windows need a later insert.
Bought polymer counterflow plate core (item A3). A plate core runs one steady fan per stream, is simple to model and build, and keeps supply and exhaust separate. The core is the part a garage builder cannot make well; a home-made crossflow core would cost about $10 but recover only about 50 to 65 % (estimate). Alternating regenerative units and enthalpy cores remain options for later variants.
Frost by slowing the supply fan (item A4). The simplest frost strategy for a 24 V unit: holding balanced flow at -10 °C with a preheater would take about 130 W. It unbalances the flows and slightly depressurizes the room (see Safety).
50 m³/h nominal with CO2-driven boost to 70 m³/h (item A5). The boost is rarely needed for R4 but costs noise (about 45 dB(A) at 70 m³/h with clean filters).
Single ESP32-C3 class controller with an SCD41 class sensor (item A6), with the sensor checked on CalRig. Quiet night mode (BBX-DDR-002). 32 m³/h per stream while people sleep, trading overnight CO2 (about 1,300 ppm) for about 30 dB(A). Larger, slower fans or a lined silencer section are to be checked against a real fan datasheet before R6 is changed; that check is on hold with TRL 4.
Larger blowers, 2 A time-delay input fuse and firmware speed cap (BBX-DDR-002), as costed and sized in BBX-CAL-001.
24 V SELV only. A certified plug-in adapter means no mains wiring for the builder (R10).

Both fans sit in the warm room-end plenum, so the exhaust side of the core runs at a slightly higher pressure than the supply side, and any core leakage would carry stale air into the supply stream. Amish decided on 2026-10-02 to keep both fans at the room end for the prototype and to add a cross-leakage check at TRL 4: a CO2 tracer in the exhaust stream, measured in the supply. The exhaust fan moves to the outdoor end only if the transfer exceeds about 3 % (BBX-DEC-001).

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
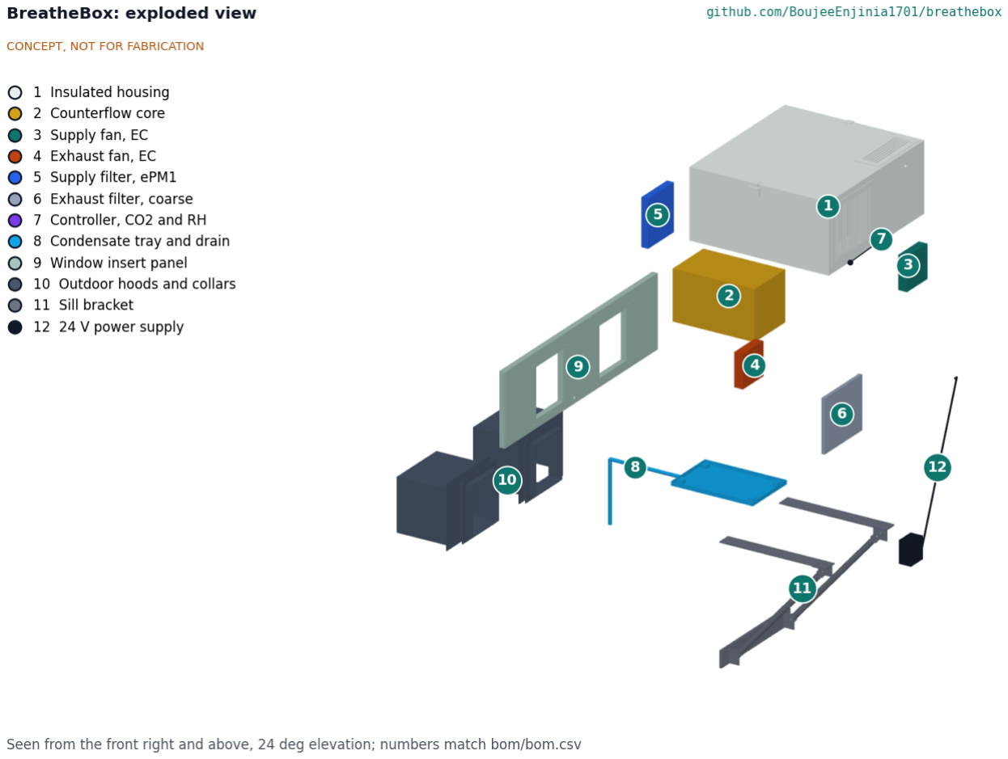
[picture p77: figure]

Figure 4. Exploded view with BOM numbers.

### Safety

Safety: Do not use BreatheBox in a room with an open-flued or unflued fuel-burning appliance (gas fire, oil or wood stove, water heater). In frost mode the unit extracts more air than it supplies and could draw combustion gases into the room. Do not install it in a room whose door seals airtight, because the depressurization would then be much larger than the 2 to 4 Pa estimated for a door with an undercut. Safety: The raised sash must be locked onto the insert panel. An unlocked sash is a security risk, and a loose panel or hood could fall outward from an upper floor. Check the bracket and panel before leaving the unit unattended, and never install from outside above ground level.
Safety: Use only a certified 24 V SELV plug-in adapter, with a 2 A time-delay fuse on the low-voltage input. Do not open or modify the adapter. Keep the cable clear of the sash and of the condensate tube.

Foam and plastics in the housing burn; choose fire-retardant grades and keep the unit away from heaters and curtains near heat sources.
Fan impellers can cut fingers: guards or grilles on both room openings, and disconnect power before opening the lid.

•

•

The drain tube can freeze outdoors in long cold spells; route it to fall continuously and check it in winter. Clean the tray and replace filters on schedule; standing water and wet filters can grow mould.
BreatheBox is a research and educational prototype, not a medical device. The CO2 reading is a ventilation indicator only and is not a health or medical measurement.

### Open questions after TRL 3

Noise: does a real fan datasheet, or a lined silencer, close the R6 gap at 50 m³/h, or should R6 be restated for the night mode?
Core: which spare-part cores are available at this size, and what are their real effectiveness and pressure drop? Fans: the chosen blower's curve, efficiency and noise data, to replace the class values in BBX-CAL-001. Airtightness: how much air leaks around the insert panel and sash, and does it matter for balance?
Window survey: what share of the first users' windows are sash, slider, casement or tilt-and-turn?

Concept media: blueprint sheet, interactive 3D model. General arrangement: BBX-DWG-001.

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
