BoujeeEnjinia1701/breathebox/cad/drawings/BBX-DWG-001.png

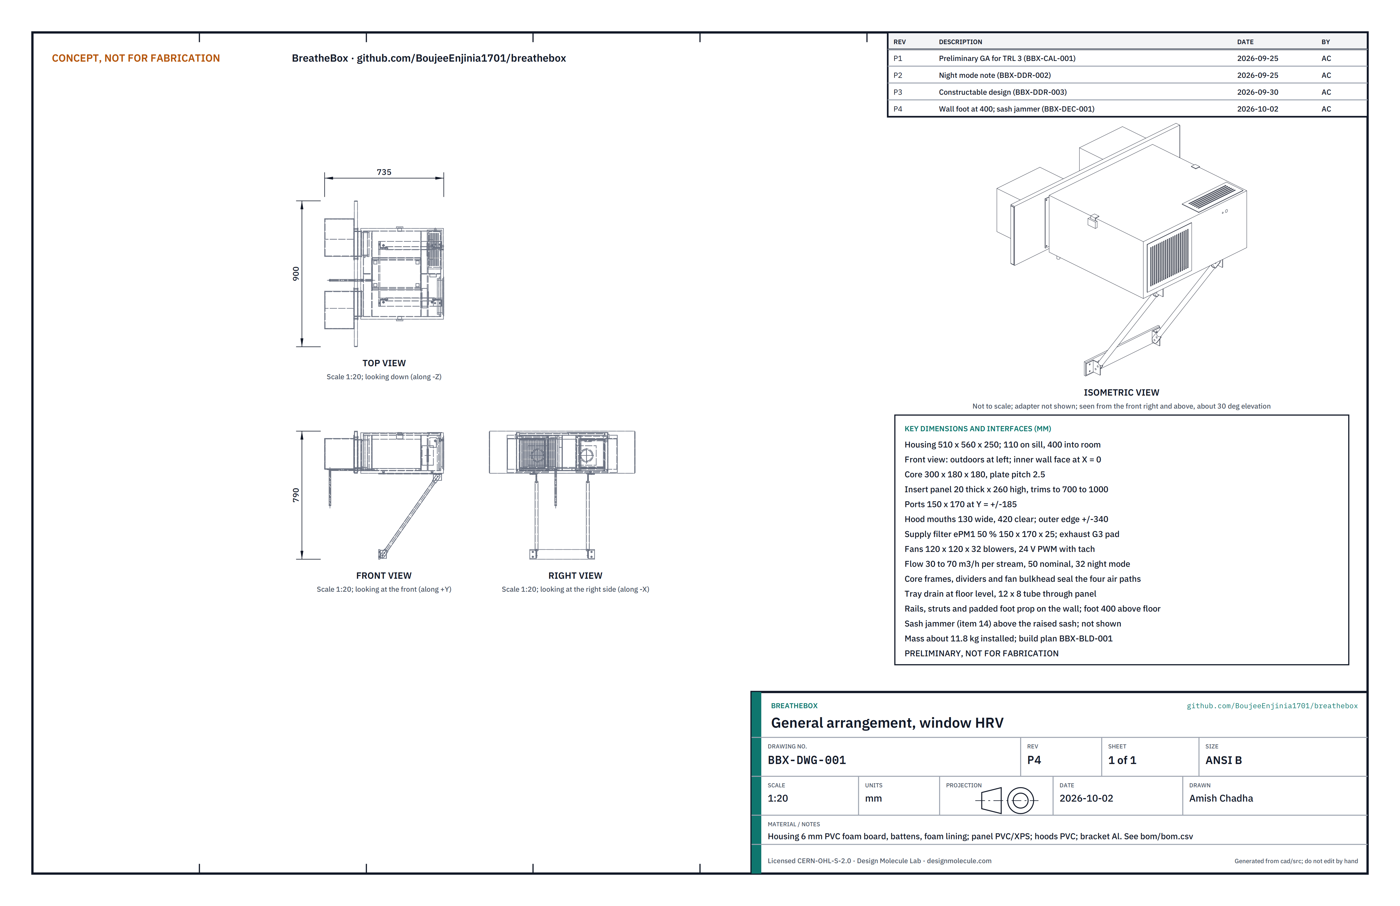
cad/drawings/BBX-DWG-001.png
