BoujeeEnjinia1701/breathebox/media/card.png

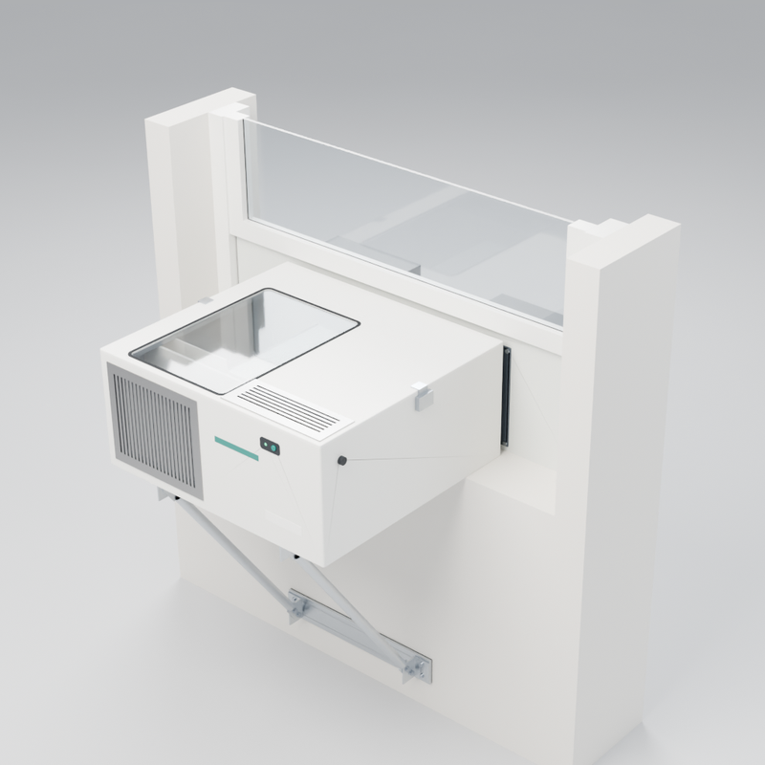
media/card.png
