BoujeeEnjinia1701/breathebox/media/render-detail.png

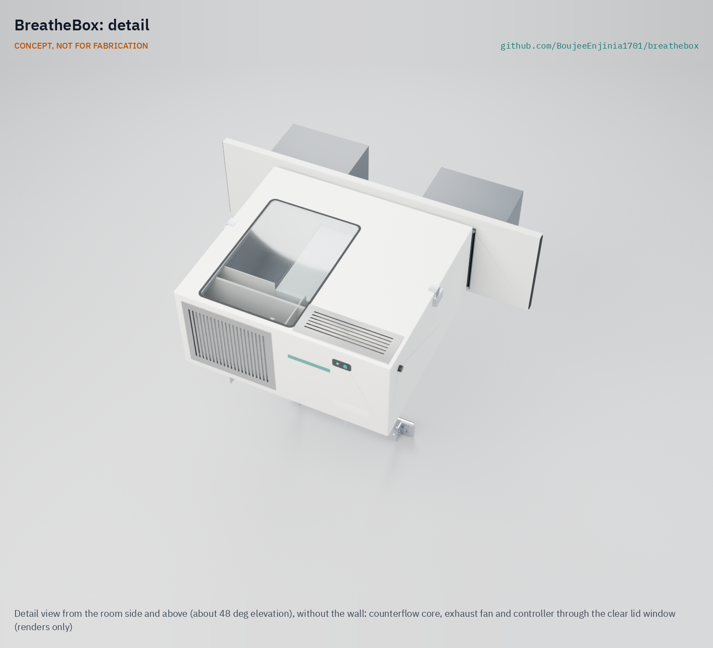
media/render-detail.png
