BoujeeEnjinia1701/breathebox/media/render-exploded.png

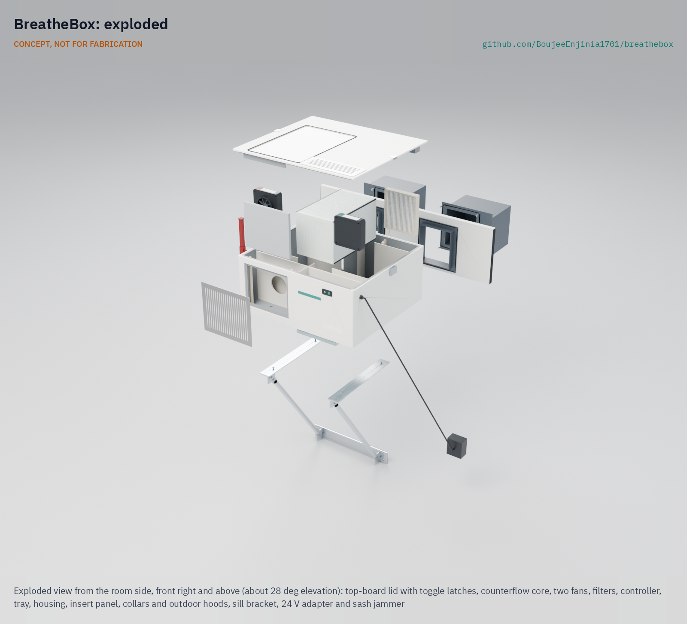
media/render-exploded.png
