BoujeeEnjinia1701/breathebox/media/social-preview.png

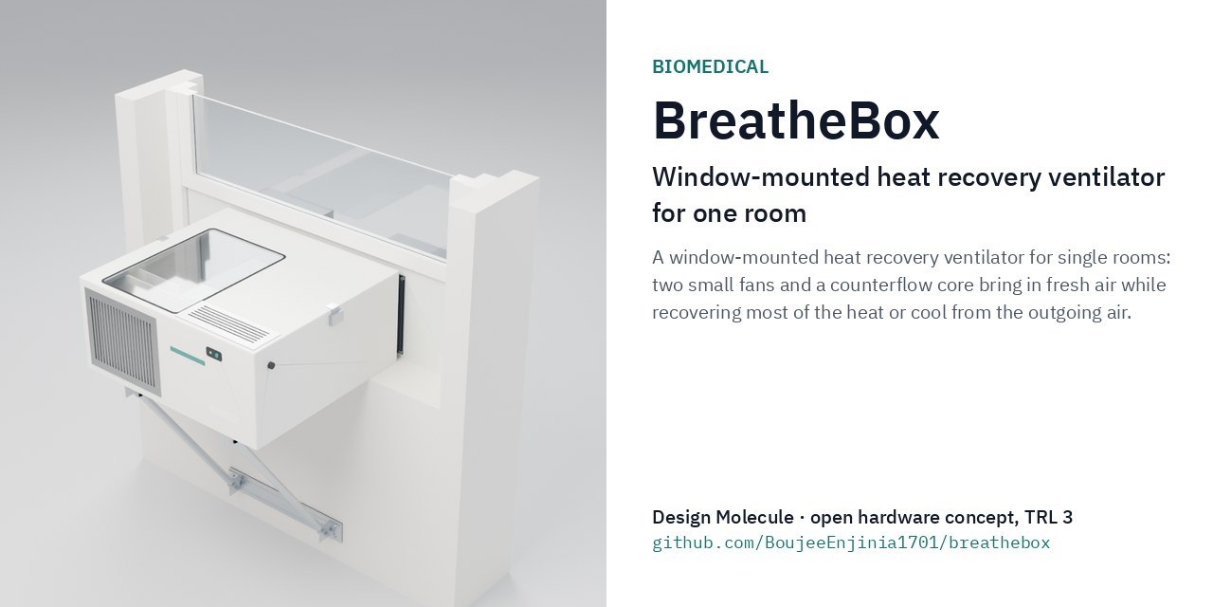
media/social-preview.png
